softegg/supercon-2023-badge-enclosure/BASIC-2/STL/Level - Supercon 2023 Badge Enclosure - BASIC-2.stl

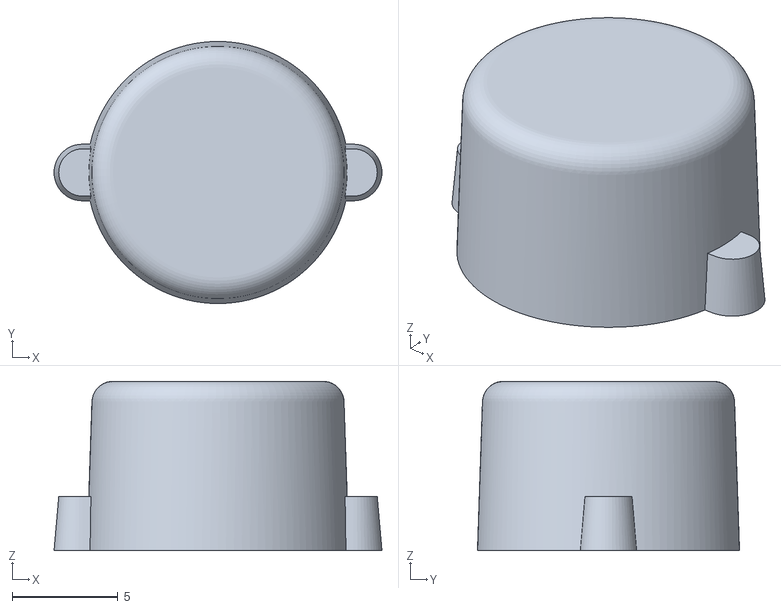
[picture p16: CAD file, 2023-10-28]
BASIC-2/STL/Level - Supercon 2023 Badge Enclosure - BASIC-2.stl
15.5 x 12.4 x 8.00
