softegg/supercon-2023-badge-enclosure/BASIC-2-HACKING/STEP/Lightpipe 1x2 A Shield - Supercon 2023 Badge Enclosure - Basic-2-Hacking.step

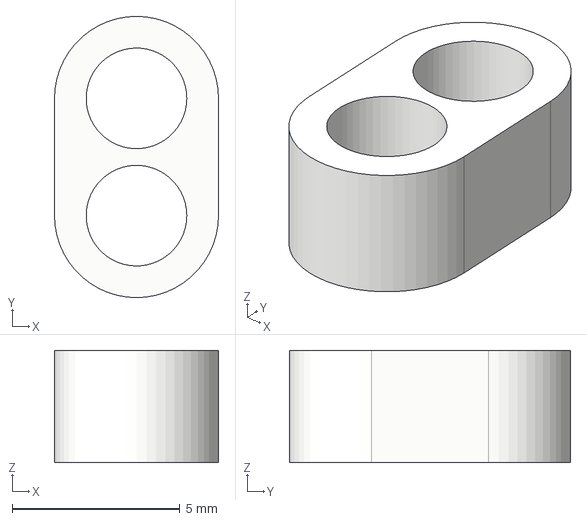
[picture p17: CAD file, 2023-10-31]
BASIC-2-HACKING/STEP/Lightpipe 1x2 A Shield - Supercon 2023 Badge Enclosure - Basic-2-Hacking.step
4.89 x 8.39 x 3.35 mm
