softegg/supercon-2023-badge-enclosure/BASIC-2-HACKING/STEP/Lightpipe 1x2 A - Supercon 2023 Badge Enclosure - Basic-2-Hacking.step

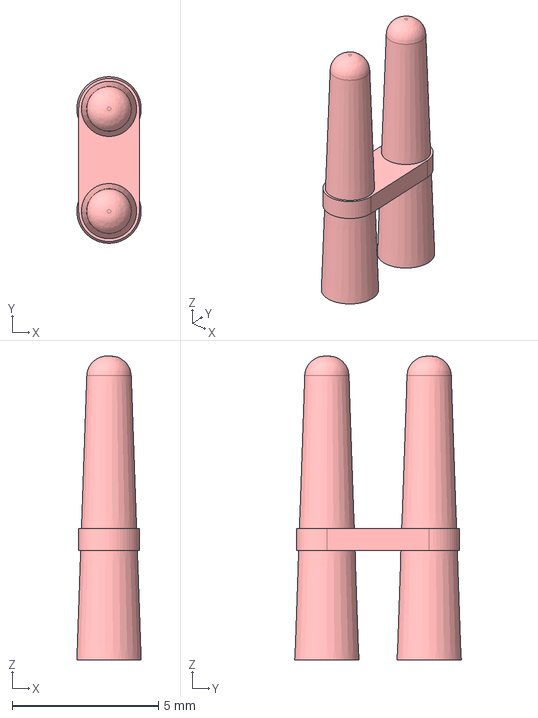
[picture p19: CAD file, 2023-10-31]
BASIC-2-HACKING/STEP/Lightpipe 1x2 A - Supercon 2023 Badge Enclosure - Basic-2-Hacking.step
2.20 x 5.70 x 10.4 mm
