softegg/supercon-2023-badge-enclosure/BASIC-2/STEP/Power Switch - Supercon 2023 Badge Enclosure - Basic-2.step

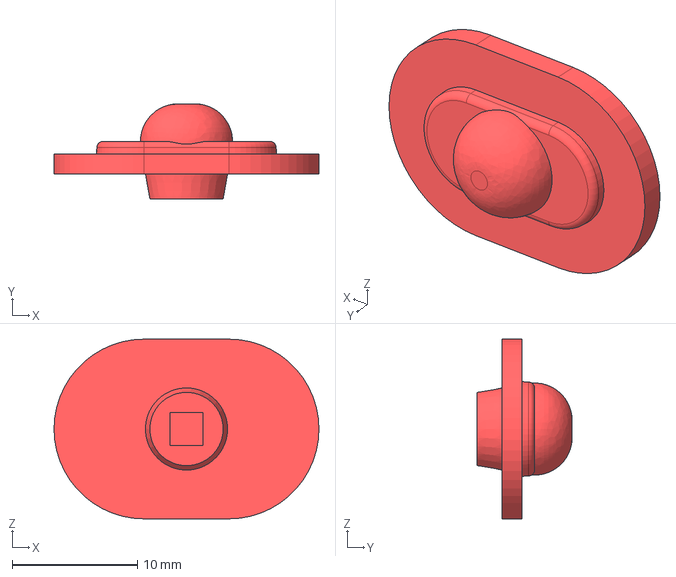
[picture p20: CAD file, 2023-10-28]
BASIC-2/STEP/Power Switch - Supercon 2023 Badge Enclosure - Basic-2.step
21.2 x 7.63 x 14.4 mm
